borislav968/swapcluster/hardware/swapcluster.kicad_sch

## KiCad design hardware/swapcluster.kicad_sch (2023-05-20)

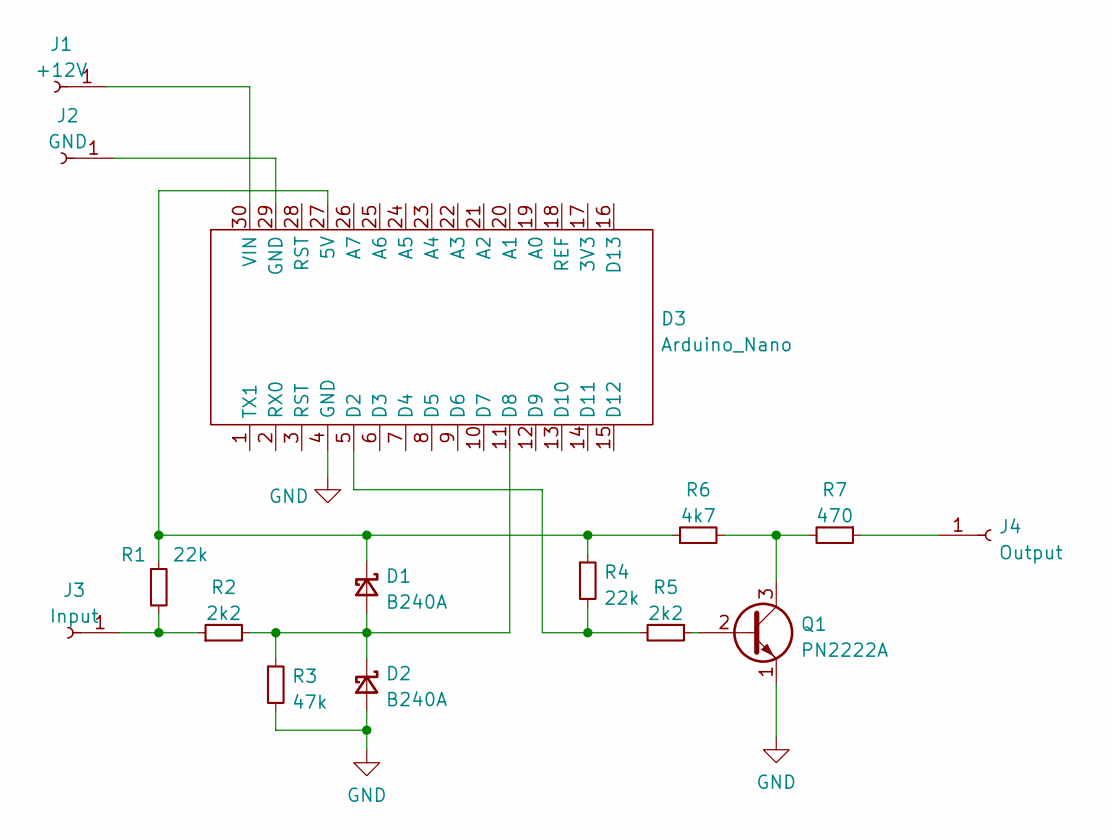
[picture p4: schematic swapcluster.kicad_sch]

Parts:
D1, D2: B240A
D3: Arduino_Nano
J1: +12V
J2: GND
J3: Input
J4: Output
Q1: PN2222A; TO-92_Inline
R1, R4: 22k
R2, R5: 2k2
R3: 47k
R6: 4k7
R7: 470

Connections:
GND: D2.2 (A), D3.4 (GND), Q1.1 (E), R3.2
unnamed: D1.1 (K), D3.27 (5V), R1.1, R4.1, R6.1
unnamed: D1.2 (A), D2.1 (K), D3.11 (D8), R2.2, R3.1
unnamed: D3.5 (D2), R4.2, R5.2
unnamed: D3.29 (GND), J2.1
unnamed: D3.30 (VIN), J1.1
unnamed: J3.1, R1.2, R2.1
unnamed: J4.1, R7.1
unnamed: Q1.2 (B), R5.1
unnamed: Q1.3 (C), R6.2, R7.2
